ViThreeDimension/voron_trident_350/documentation_subpages/btt_octopus_pro_1.0_pins.png

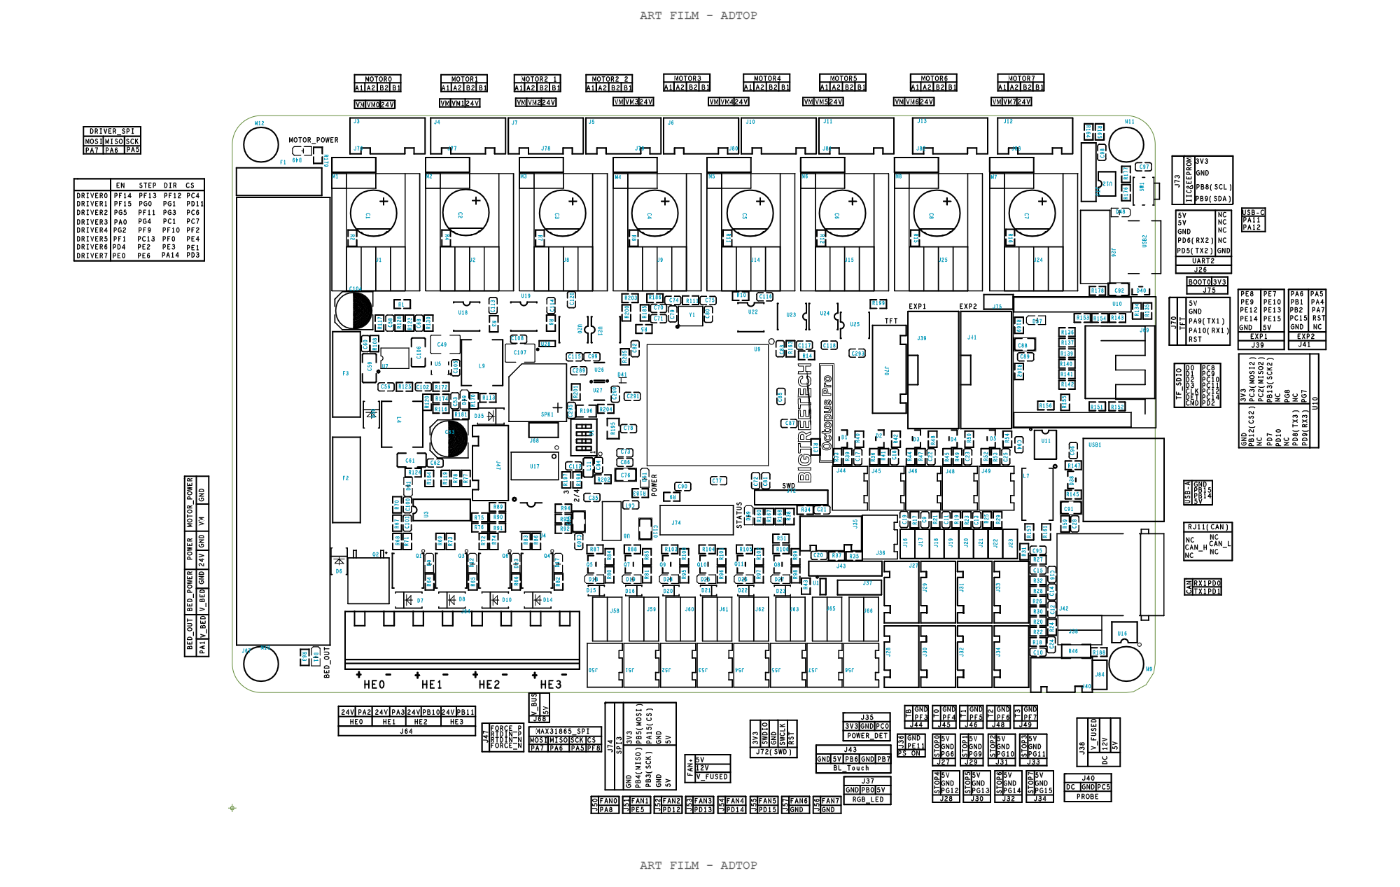
documentation_subpages/btt_octopus_pro_1.0_pins.png
