ViThreeDimension/voron_trident_350/mods/Sherpa_Mini-Extruder-master/Images/sherpa_mini_rc1.jpg

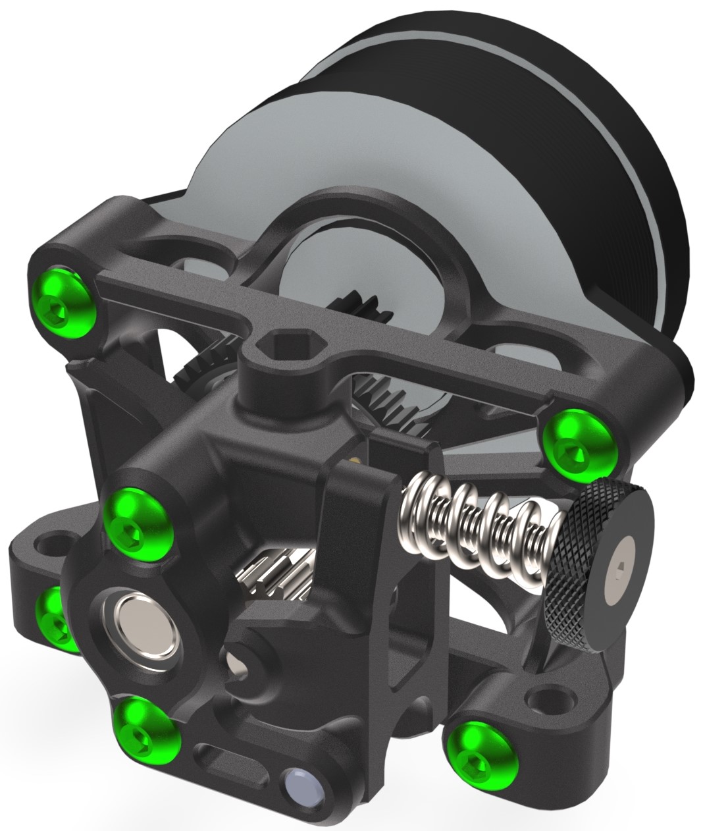
mods/Sherpa_Mini-Extruder-master/Images/sherpa_mini_rc1.jpg
