ViThreeDimension/voron_trident_350/mods/STH-36_sherpa_mini_mounting_plate_overmold_strain.stl

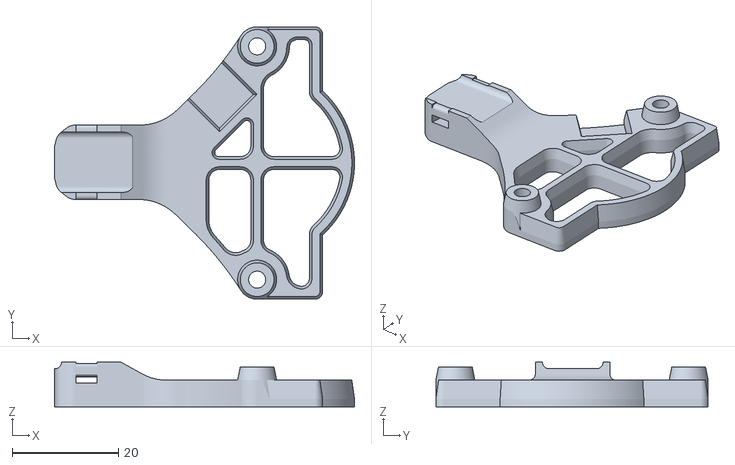
[picture p25: CAD file, 2022-10-18]
mods/STH-36_sherpa_mini_mounting_plate_overmold_strain.stl
56.4 x 51.2 x 8.36
