ViThreeDimension/voron_trident_350/mods/front panel handle/Front Panel - Handle Frame.3mf

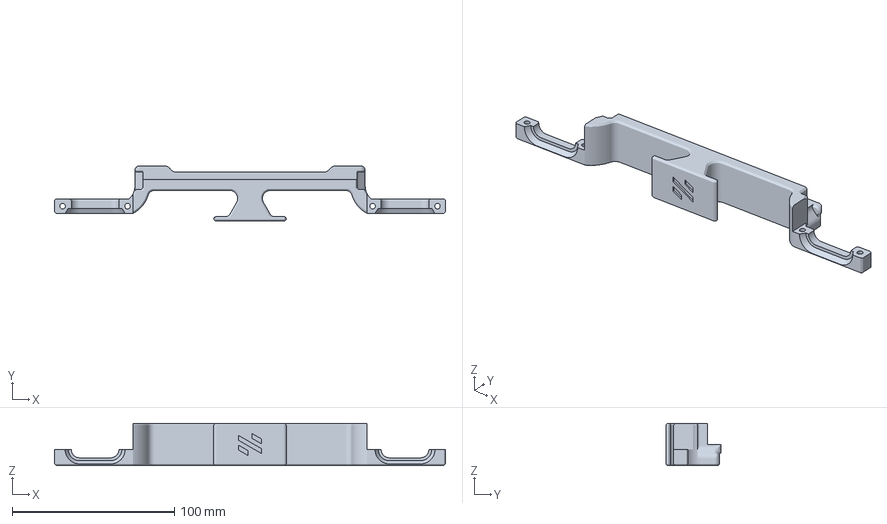
[picture p26: CAD file, 2022-12-22]
mods/front panel handle/Front Panel - Handle Frame.3mf
241.0 x 34.2 x 26.0 mm
