ViThreeDimension/voron_trident_350/mods/klickyNG/KlickyNG_Probe_Dock.stl

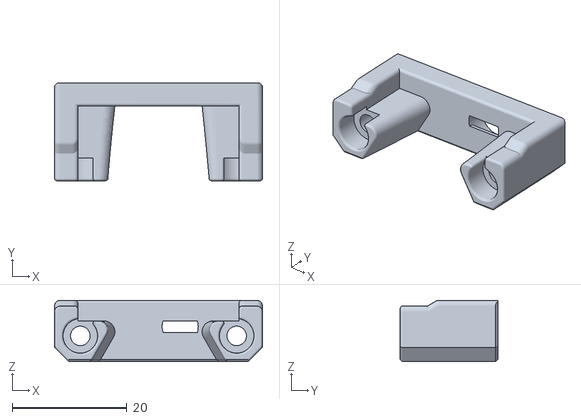
[picture p27: CAD file, 2022-10-18]
mods/klickyNG/KlickyNG_Probe_Dock.stl
36.3 x 17.0 x 10.7
