ViThreeDimension/voron_trident_350/mods/klickyNG/STL/2mm_extender.stl

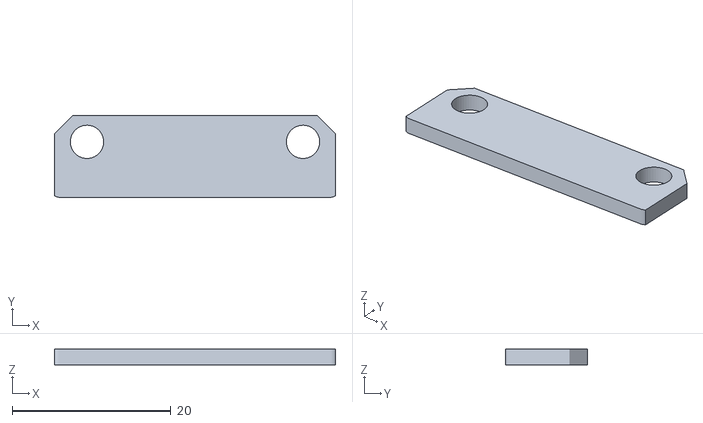
[picture p28: CAD file, 2022-10-18]
mods/klickyNG/STL/2mm_extender.stl
35.5 x 10.3 x 2.00
