ViThreeDimension/voron_trident_350/mods/own mods/Trident Carbon Pin Mod/a_drive_frame_upper_pinned.3mf

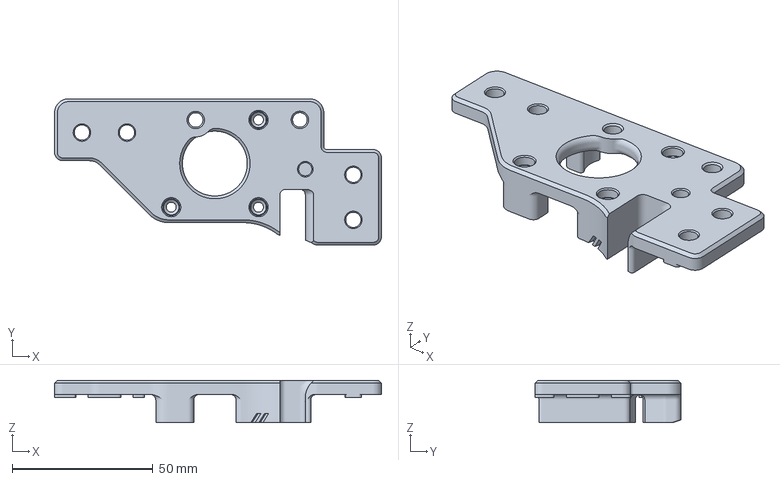
[picture p29: CAD file, 2022-10-18]
mods/own mods/Trident Carbon Pin Mod/a_drive_frame_upper_pinned.3mf
116.2 x 52.0 x 15.0 mm
