ViThreeDimension/voron_trident_350/mods/Panel_Locker/Locker_6mm.stl

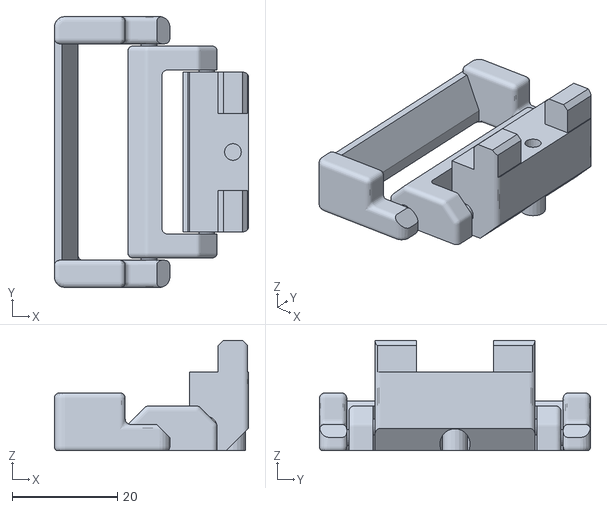
[picture p31: CAD file, 2022-10-18]
mods/Panel_Locker/Locker_6mm.stl
37.0 x 51.6 x 21.0
