ViThreeDimension/voron_trident_350/mods/Panel_Locker/step/Thin_PanelLocker.stp

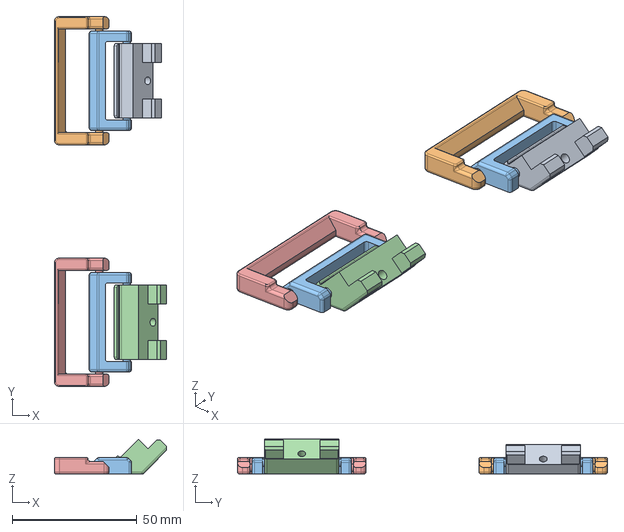
[picture p32: CAD file, 2022-10-18]
mods/Panel_Locker/step/Thin_PanelLocker.stp
45.1 x 148.6 x 13.9 mm
