ViThreeDimension/voron_trident_350/mods/Panel_Locker/Thin Locker/Thin_Locker_6.5mm.stl

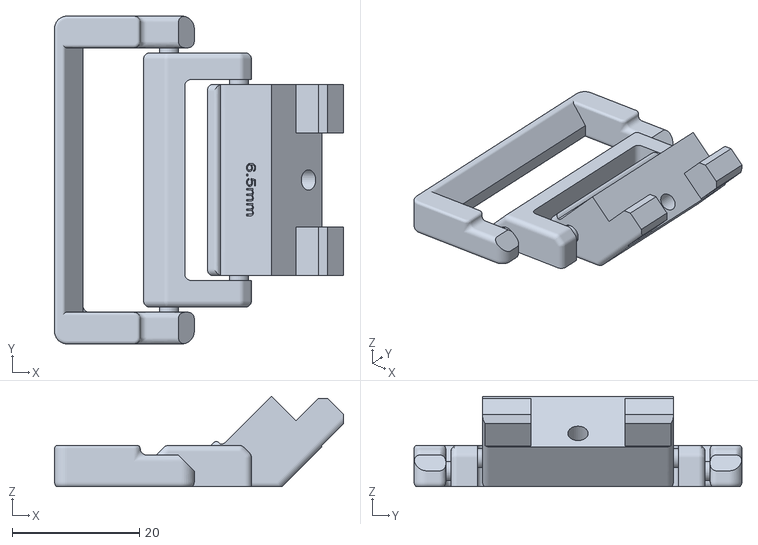
[picture p33: CAD file, 2022-10-18]
mods/Panel_Locker/Thin Locker/Thin_Locker_6.5mm.stl
45.5 x 51.6 x 14.2
