ViThreeDimension/voron_trident_350/mods/Sherpa_Mini-Extruder-master/Assembly_Tools/Shaft_Grinding_Tool/bottom.stl

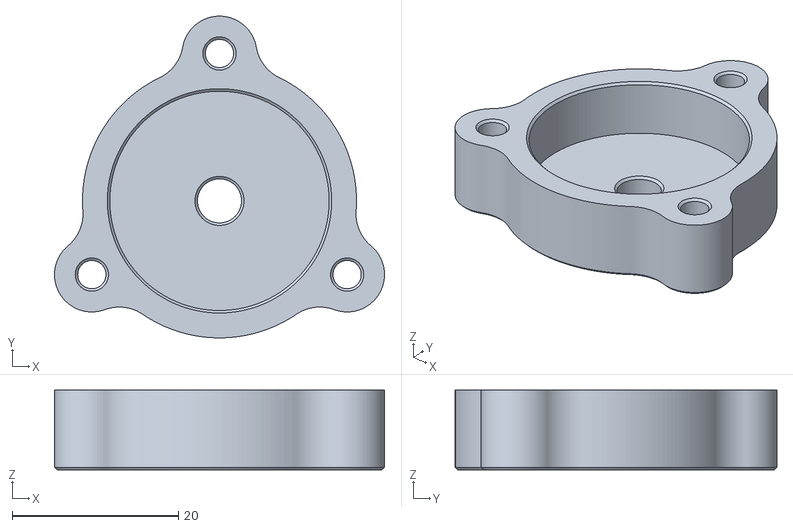
[picture p34: CAD file, 2022-10-18]
mods/Sherpa_Mini-Extruder-master/Assembly_Tools/Shaft_Grinding_Tool/bottom.stl
39.7 x 38.7 x 9.60
