ViThreeDimension/voron_trident_350/mods/Sherpa_Mini-Extruder-master/STLs/experimental_SLS+MJF_STLs/sls_[a]_idler_arm_long_x1_rev1.STL

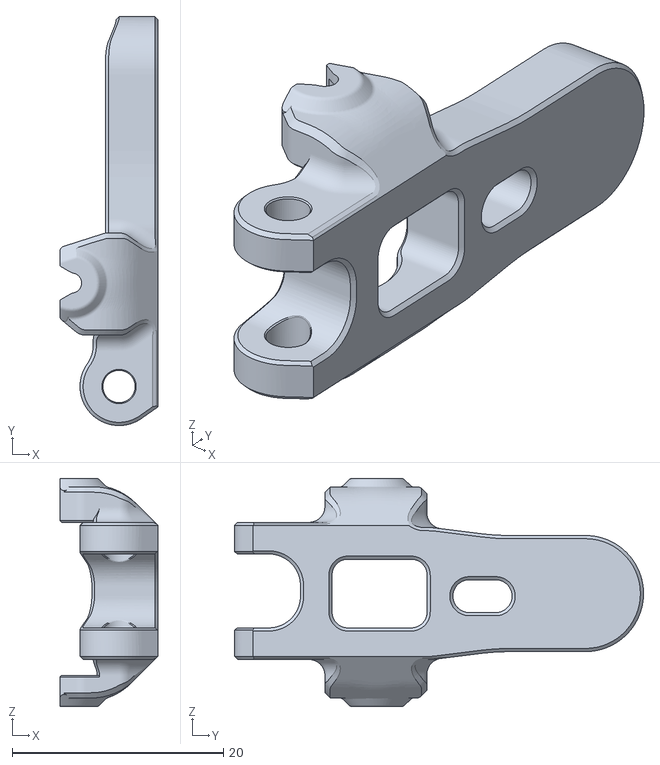
[picture p35: CAD file, 2022-10-18]
mods/Sherpa_Mini-Extruder-master/STLs/experimental_SLS+MJF_STLs/sls_[a]_idler_arm_long_x1_rev1.STL
9.30 x 38.8 x 21.6
