ViThreeDimension/voron_trident_350/mods/Sherpa_Mini-Extruder-master/STLs/FDM_STLs/optional_parts/rappel_adapter_x1_rev1.stl

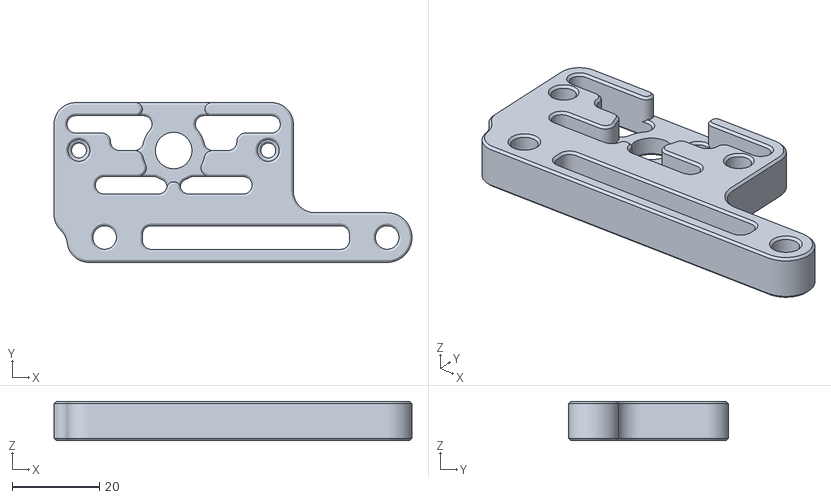
[picture p36: CAD file, 2022-10-18]
mods/Sherpa_Mini-Extruder-master/STLs/FDM_STLs/optional_parts/rappel_adapter_x1_rev1.stl
82.3 x 36.7 x 9.00
