ViThreeDimension/voron_trident_350/mods/front panel handle/panel vhb bottom.3mf

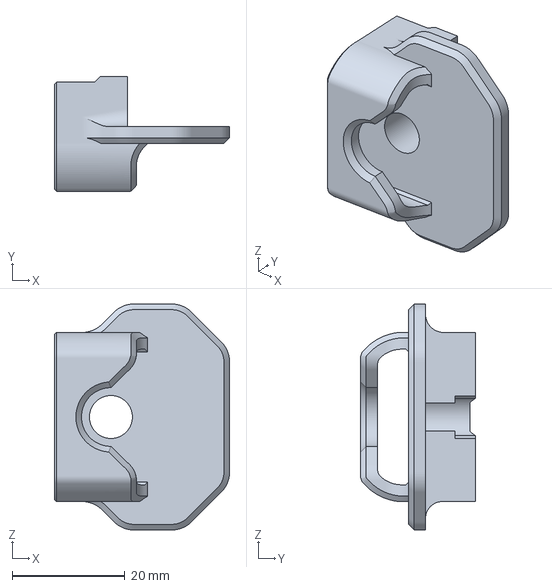
[picture p37: CAD file, 2022-12-22]
mods/front panel handle/panel vhb bottom.3mf
31.0 x 20.3 x 40.0 mm
