ViThreeDimension/voron_trident_350/mods/klickyNG/STL/KlickyNG_Tiny-M_mount_base.stl

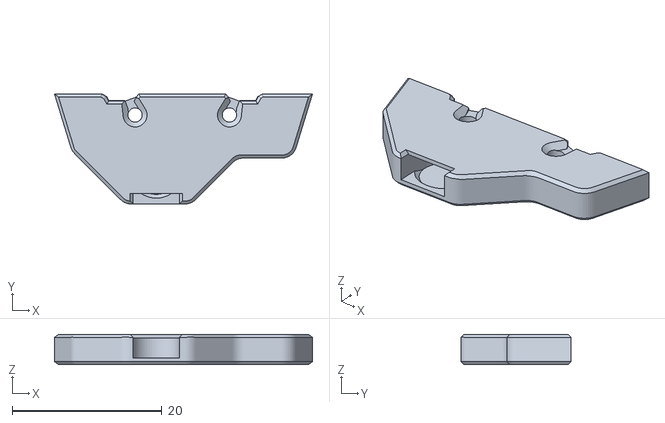
[picture p38: CAD file, 2022-10-18]
mods/klickyNG/STL/KlickyNG_Tiny-M_mount_base.stl
34.4 x 14.7 x 4.03
