ViThreeDimension/voron_trident_350/mods/own mods/RS25_psu_bracket_wide.step

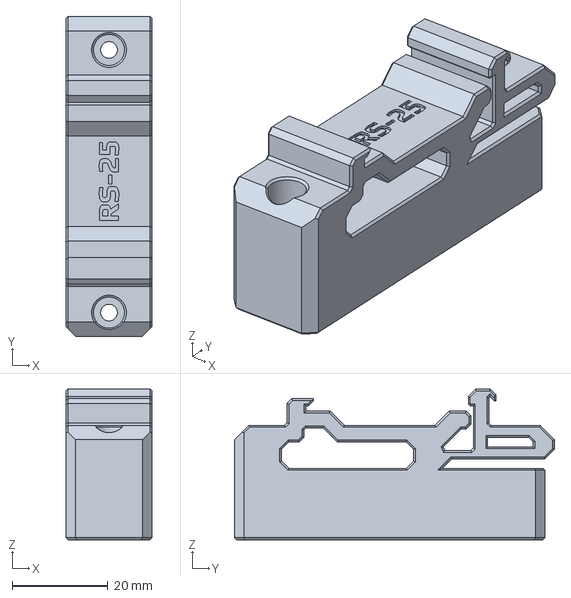
[picture p39: CAD file, 2022-12-22]
mods/own mods/RS25_psu_bracket_wide.step
18.0 x 67.0 x 31.6 mm
