ViThreeDimension/voron_trident_350/mods/own mods/Trident Pin Mod/STLs/b_drive_frame_lower_pinned.stl

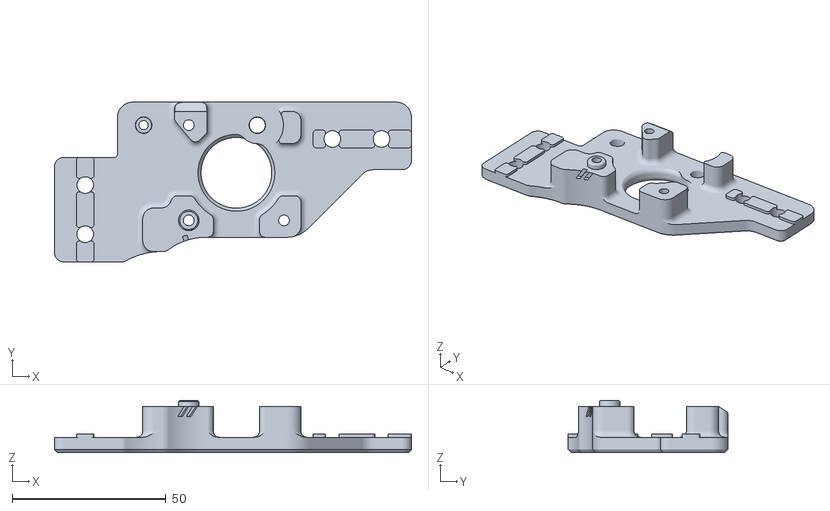
[picture p40: CAD file, 2022-10-18]
mods/own mods/Trident Pin Mod/STLs/b_drive_frame_lower_pinned.stl
116.2 x 52.0 x 17.0
