ViThreeDimension/voron_trident_350/mods/Panel_Locker/Thin Locker/Thin_Locker_5.5mm.stl

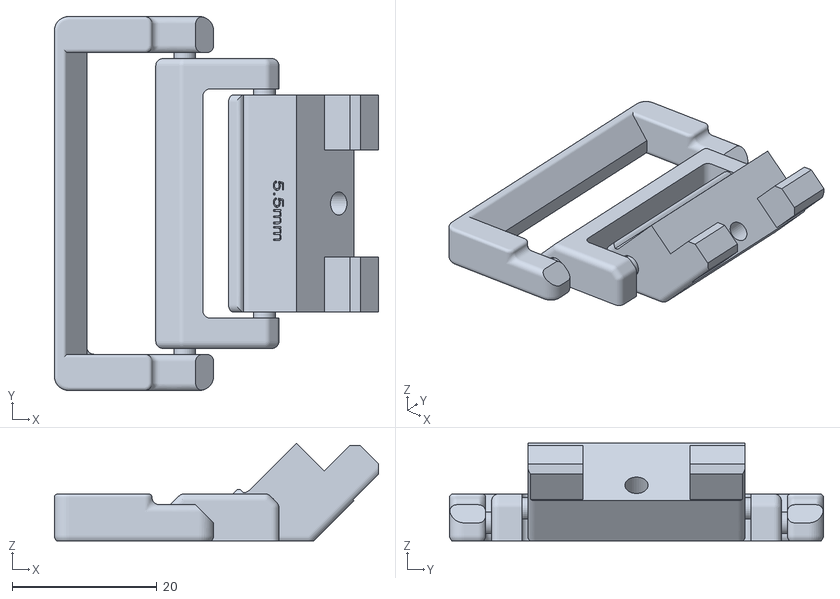
[picture p41: CAD file, 2022-10-18]
mods/Panel_Locker/Thin Locker/Thin_Locker_5.5mm.stl
44.8 x 51.6 x 13.5
