ViThreeDimension/voron_trident_350/mods/Sherpa_Mini-Extruder-master/Assembly_Tools/Shaft_Grinding_Tool/shaft_block v4.step

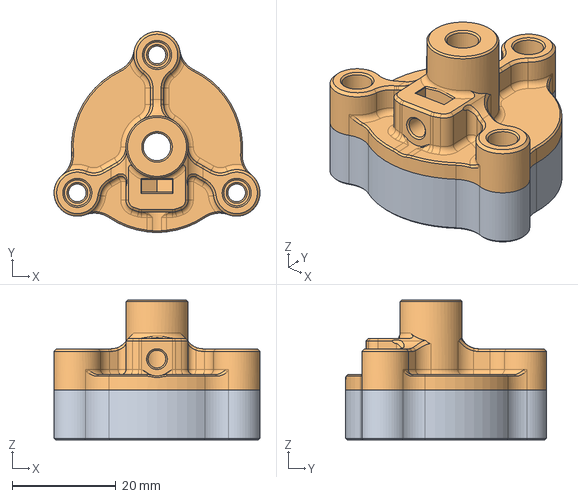
[picture p42: CAD file, 2022-10-18]
mods/Sherpa_Mini-Extruder-master/Assembly_Tools/Shaft_Grinding_Tool/shaft_block v4.step
39.8 x 38.8 x 27.0 mm
bottom
top
