ViThreeDimension/voron_trident_350/mods/Sherpa_Mini-Extruder-master/STLs/FDM_STLs/optional_parts/[a]_housing_front_k_x1_rev5.STL

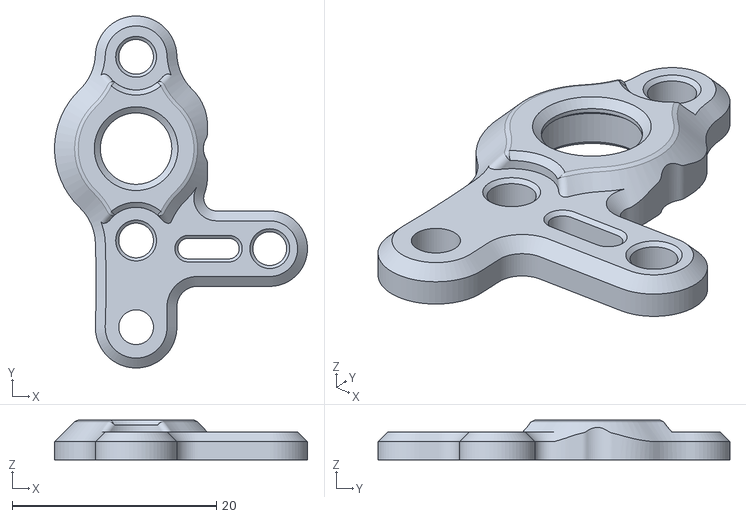
[picture p43: CAD file, 2022-10-18]
mods/Sherpa_Mini-Extruder-master/STLs/FDM_STLs/optional_parts/[a]_housing_front_k_x1_rev5.STL
24.8 x 34.5 x 3.90
