ViThreeDimension/voron_trident_350/mods/front panel handle/BottomFrontPanel_extraSized.3mf

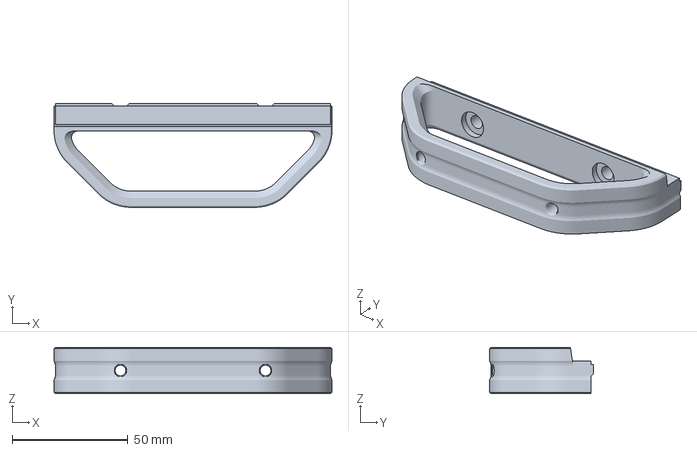
[picture p44: CAD file, 2022-12-22]
mods/front panel handle/BottomFrontPanel_extraSized.3mf
120.0 x 44.8 x 20.0 mm
