ViThreeDimension/voron_trident_350/mods/klickyNG/STL/KlickyNG_Probe_insert.stl

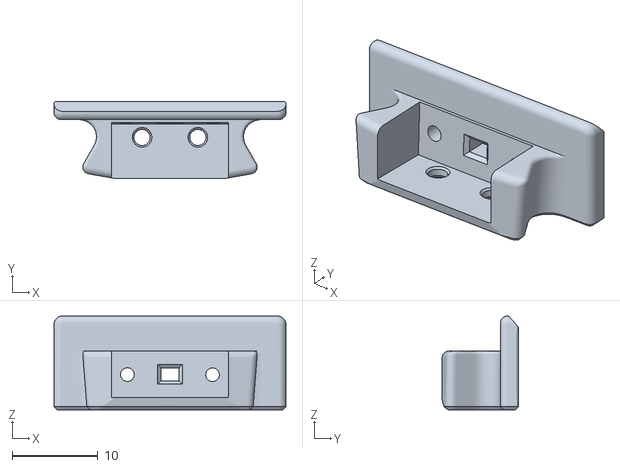
[picture p45: CAD file, 2022-10-18]
mods/klickyNG/STL/KlickyNG_Probe_insert.stl
27.0 x 8.97 x 11.0
