ViThreeDimension/voron_trident_350/mods/own mods/Trident Pin Mod/STLs/[a]_tensioner_left_pinned.stl

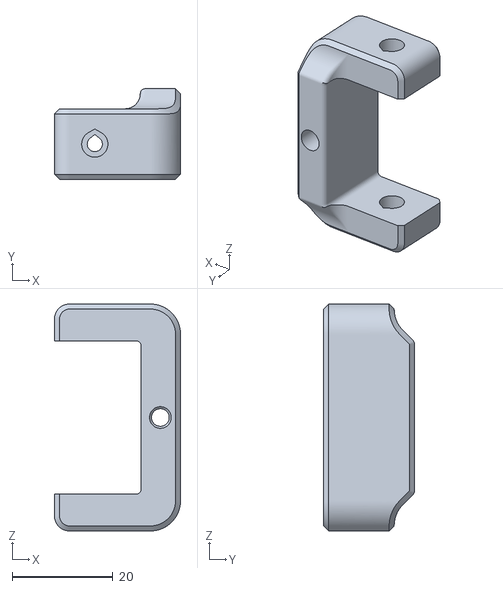
[picture p47: CAD file, 2022-10-18]
mods/own mods/Trident Pin Mod/STLs/[a]_tensioner_left_pinned.stl
25.0 x 18.0 x 45.0
