ViThreeDimension/voron_trident_350/mods/Panel_Locker/Thin Locker/Thin_Locker_3mm.stl

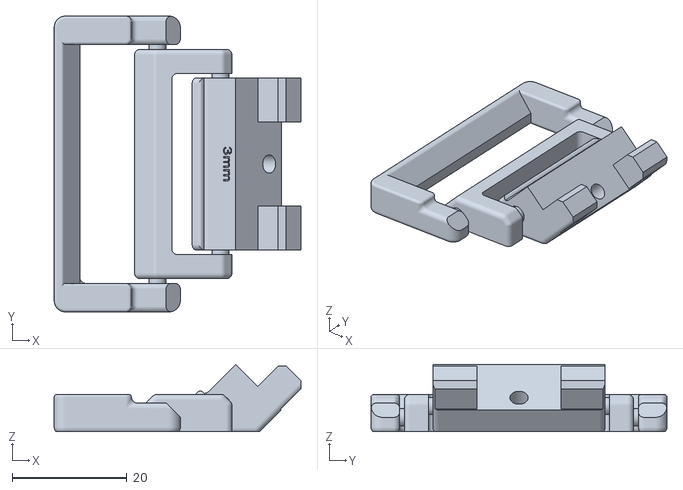
[picture p48: CAD file, 2022-10-18]
mods/Panel_Locker/Thin Locker/Thin_Locker_3mm.stl
43.0 x 51.6 x 11.7
