ViThreeDimension/voron_trident_350/mods/Sherpa_Mini-Extruder-master/STLs/FDM_STLs/housing_front_angled_front_brace.stl

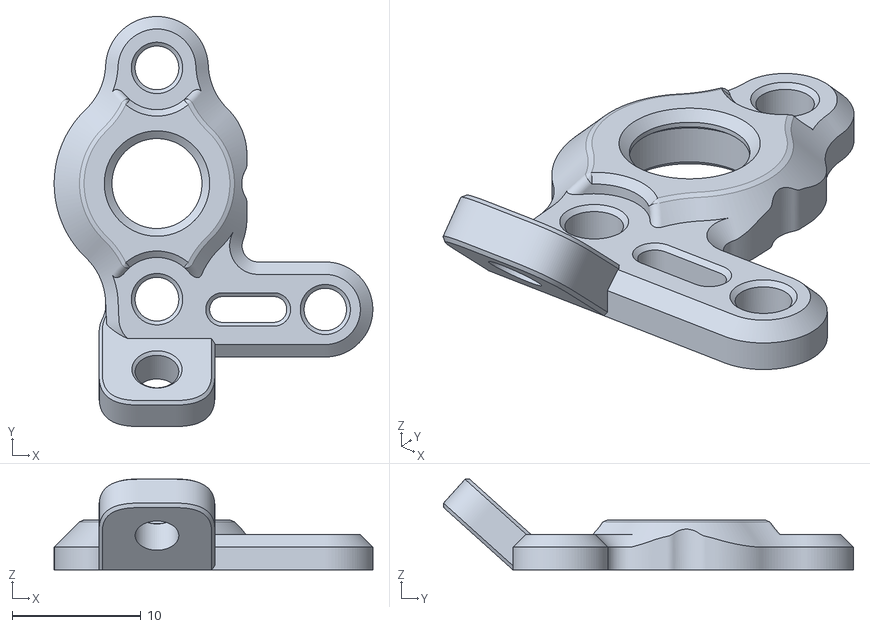
[picture p49: CAD file, 2022-10-18]
mods/Sherpa_Mini-Extruder-master/STLs/FDM_STLs/housing_front_angled_front_brace.stl
24.8 x 31.9 x 7.08
