ViThreeDimension/voron_trident_350/mods/Sherpa_Mini-Extruder-master/STLs/FDM_STLs/optional_parts/printable_sherpa_mini_gear_50t_sl_x1_rev1.stl

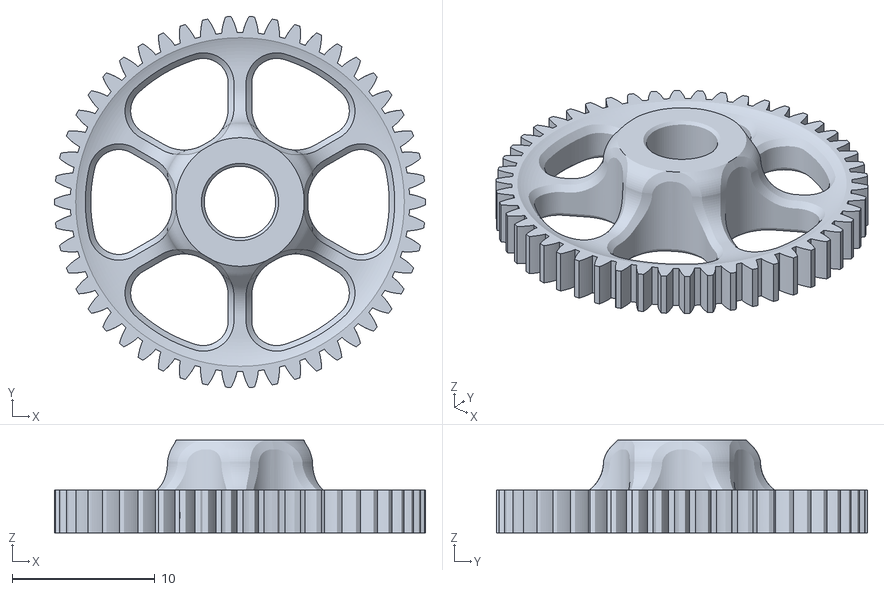
[picture p50: CAD file, 2022-10-18]
mods/Sherpa_Mini-Extruder-master/STLs/FDM_STLs/optional_parts/printable_sherpa_mini_gear_50t_sl_x1_rev1.stl
26.0 x 26.0 x 6.50
