ViThreeDimension/voron_trident_350/mods/front panel handle/Front Panel - RHS Latch.3mf

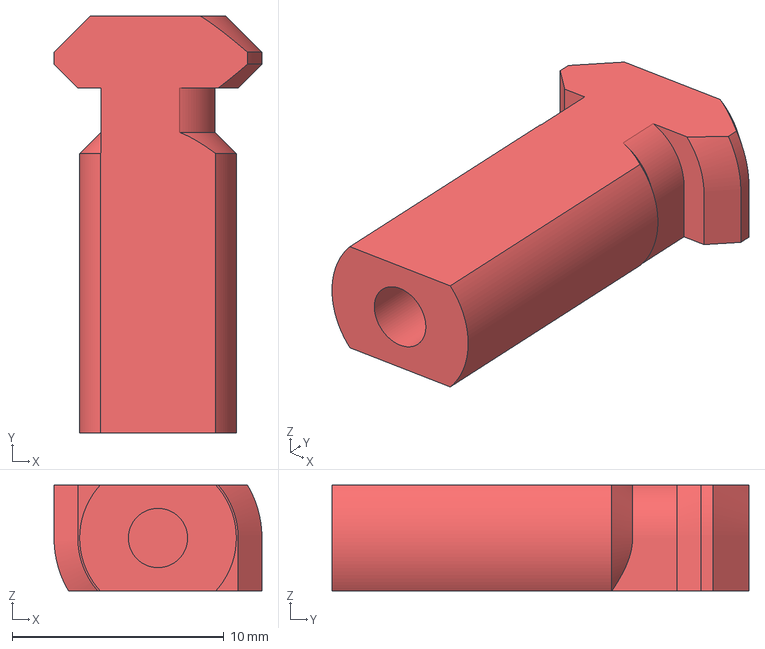
[picture p51: CAD file, 2022-12-22]
mods/front panel handle/Front Panel - RHS Latch.3mf
9.82 x 19.7 x 5.00 mm
