ViThreeDimension/voron_trident_350/mods/klickyNG/STL/KlickyNG_ABSB_mount_front.stl

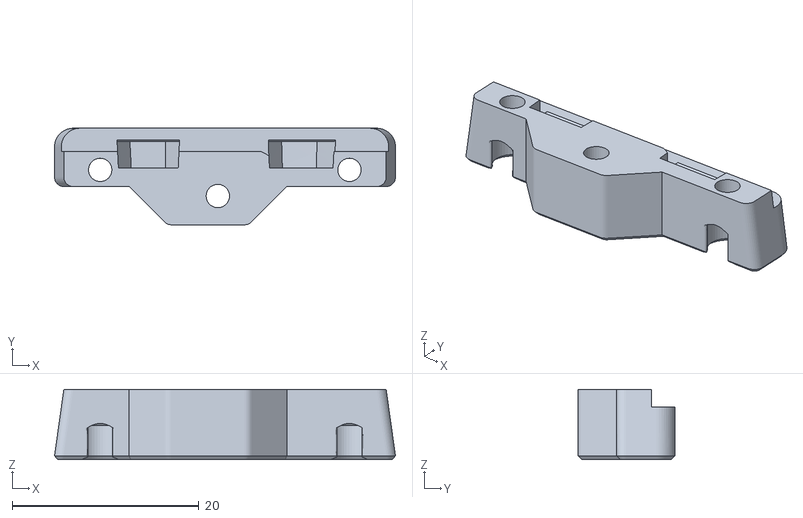
[picture p52: CAD file, 2022-10-18]
mods/klickyNG/STL/KlickyNG_ABSB_mount_front.stl
36.5 x 10.4 x 7.50
