ViThreeDimension/voron_trident_350/mods/Panel_Locker/Locker_3mm.stl

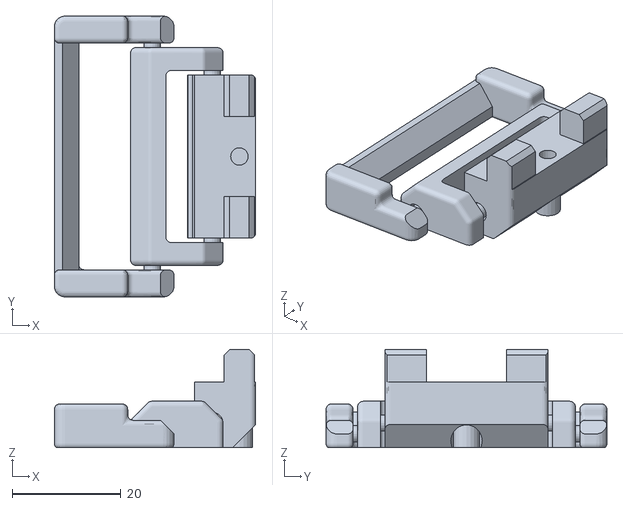
[picture p53: CAD file, 2022-10-18]
mods/Panel_Locker/Locker_3mm.stl
37.0 x 51.6 x 18.0
