ViThreeDimension/voron_trident_350/mods/Panel_Locker/Thin Locker/Thin_Locker_7.5mm.stl

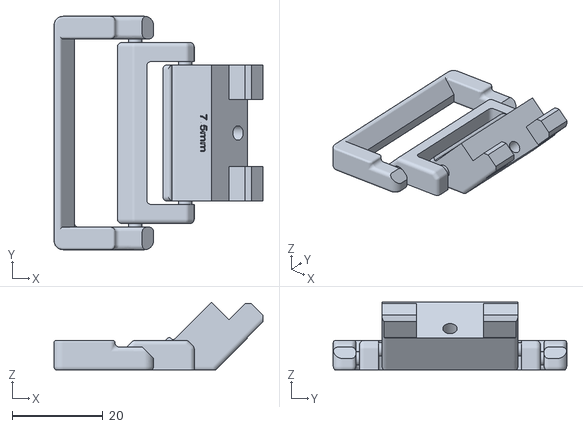
[picture p54: CAD file, 2022-10-18]
mods/Panel_Locker/Thin Locker/Thin_Locker_7.5mm.stl
46.2 x 51.6 x 14.9
