ViThreeDimension/voron_trident_350/mods/front panel handle/panel vhb.3mf

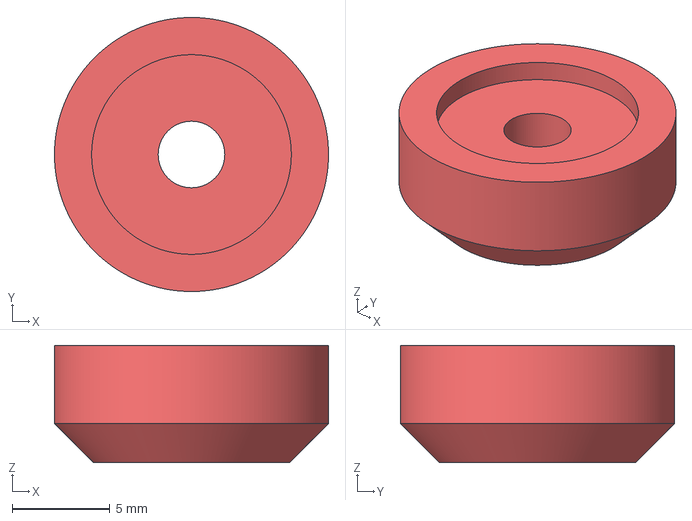
[picture p55: CAD file, 2022-12-22]
mods/front panel handle/panel vhb.3mf
14.0 x 14.0 x 6.00 mm
