ViThreeDimension/voron_trident_350/mods/own mods/Trident Pin Mod/STLs/xy_joint_left_upper_MGN12_pinned.stl

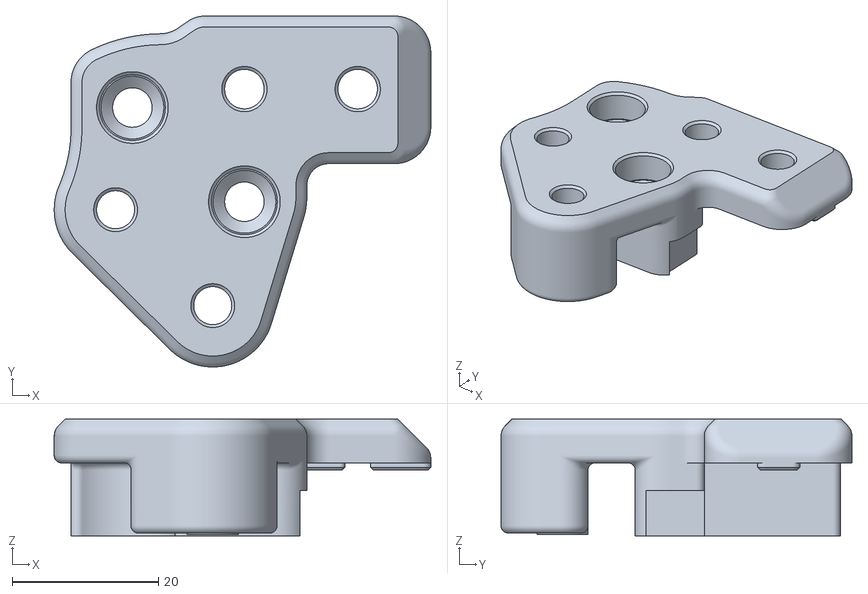
[picture p56: CAD file, 2022-10-18]
mods/own mods/Trident Pin Mod/STLs/xy_joint_left_upper_MGN12_pinned.stl
51.5 x 48.0 x 16.0
