ViThreeDimension/voron_trident_350/mods/Panel_Locker/Thin Locker/Thin_Locker_3.5mm.stl

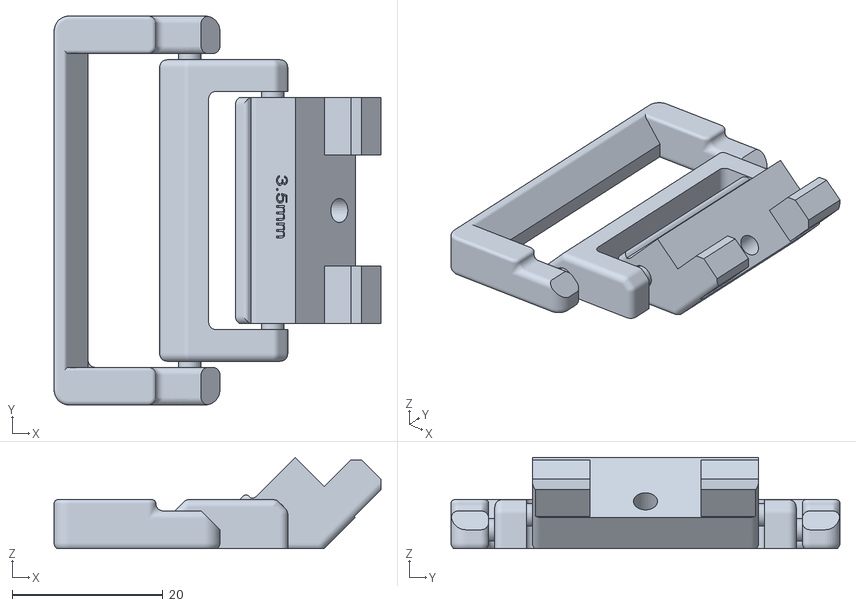
[picture p57: CAD file, 2022-10-18]
mods/Panel_Locker/Thin Locker/Thin_Locker_3.5mm.stl
43.4 x 51.6 x 12.1
