ViThreeDimension/voron_trident_350/mods/front panel handle/Front Panel - RHS Lever - with Pin.3mf

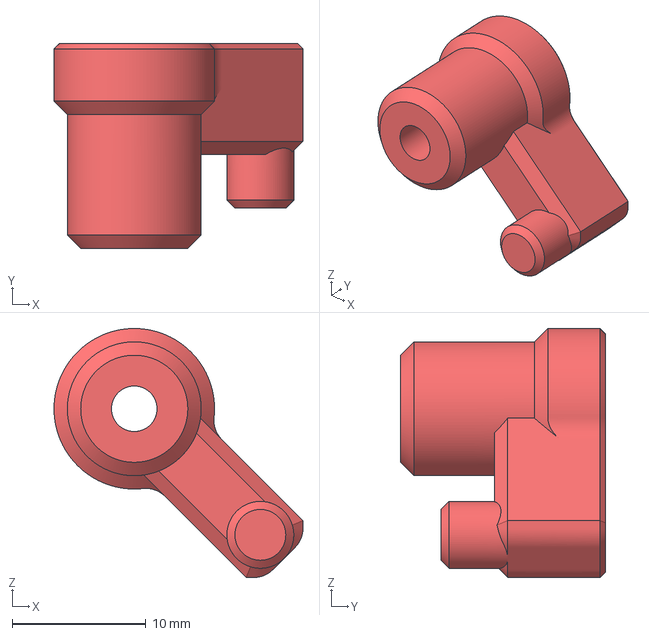
[picture p58: CAD file, 2022-12-22]
mods/front panel handle/Front Panel - RHS Lever - with Pin.3mf
18.6 x 15.3 x 18.6 mm
