ViThreeDimension/voron_trident_350/mods/Panel_Locker/Thin Locker/Thin_Locker_6mm.stl

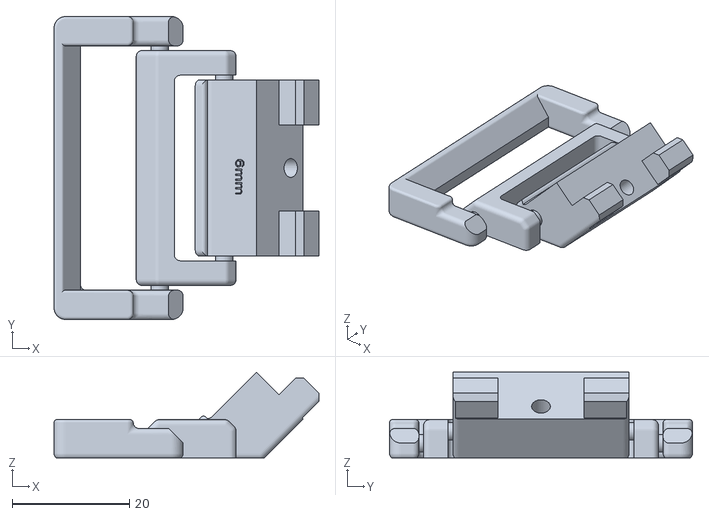
[picture p60: CAD file, 2022-10-18]
mods/Panel_Locker/Thin Locker/Thin_Locker_6mm.stl
45.1 x 51.6 x 14.6
