ViThreeDimension/voron_trident_350/mods/klickyNG/STL/KlickyNG_Tiny-M_mount_front.stl

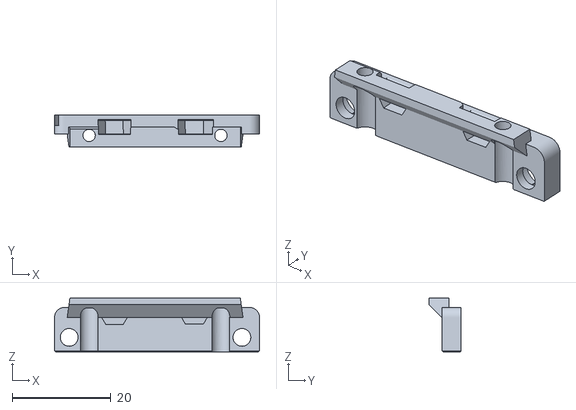
[picture p61: CAD file, 2022-10-18]
mods/klickyNG/STL/KlickyNG_Tiny-M_mount_front.stl
41.5 x 6.54 x 10.9
