ViThreeDimension/voron_trident_350/mods/Panel_Locker/Thin Locker/Thin_Locker_4.5mm.stl

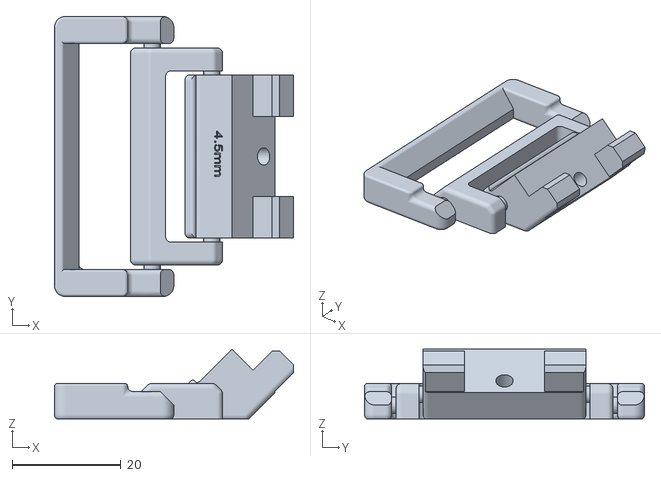
[picture p62: CAD file, 2022-10-18]
mods/Panel_Locker/Thin Locker/Thin_Locker_4.5mm.stl
44.1 x 51.6 x 12.8
