ViThreeDimension/voron_trident_350/mods/klickyNG/STL/KlickyNG_Probe_Helper_mount.stl

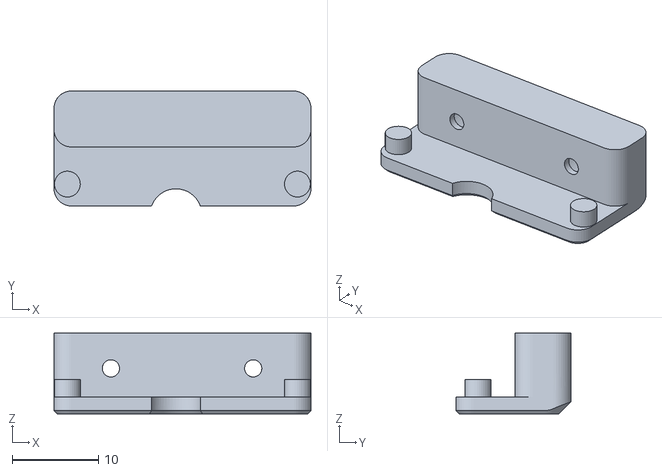
[picture p63: CAD file, 2022-10-18]
mods/klickyNG/STL/KlickyNG_Probe_Helper_mount.stl
29.8 x 13.3 x 9.40
