ViThreeDimension/voron_trident_350/mods/Panel_Locker/Thin Locker/Thin_Locker_4mm.stl

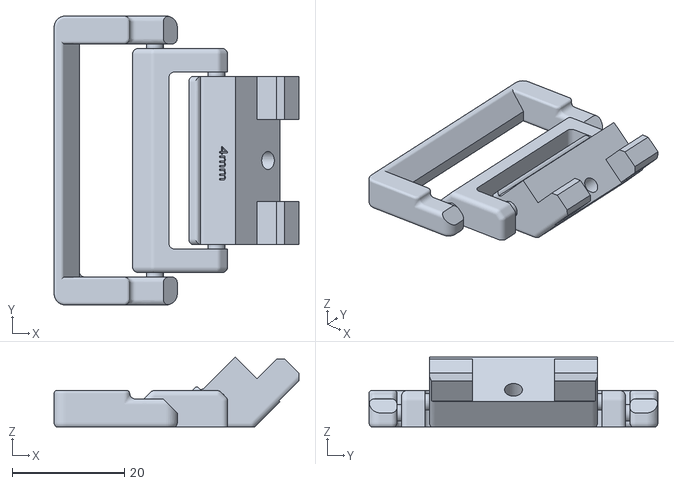
[picture p64: CAD file, 2022-10-18]
mods/Panel_Locker/Thin Locker/Thin_Locker_4mm.stl
43.7 x 51.6 x 12.5
