ViThreeDimension/voron_trident_350/mods/klickyNG/STL/KlickyNG_Probe_body.stl

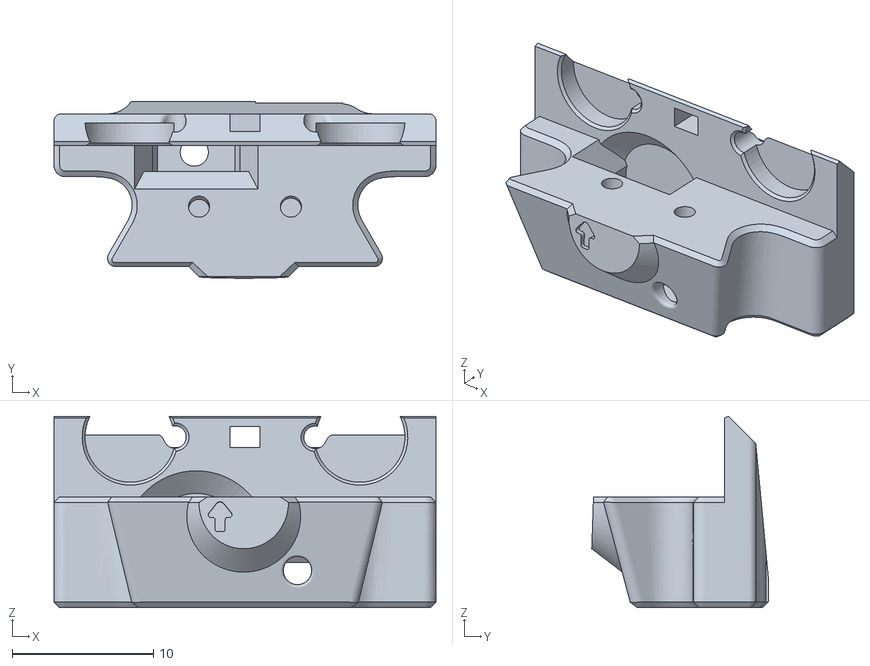
[picture p65: CAD file, 2022-10-18]
mods/klickyNG/STL/KlickyNG_Probe_body.stl
27.0 x 12.5 x 13.5
