ViThreeDimension/voron_trident_350/mods/Sherpa_Mini-Extruder-master/Assembly_Tools/Shaft_Grinding_Tool/tool_2.png

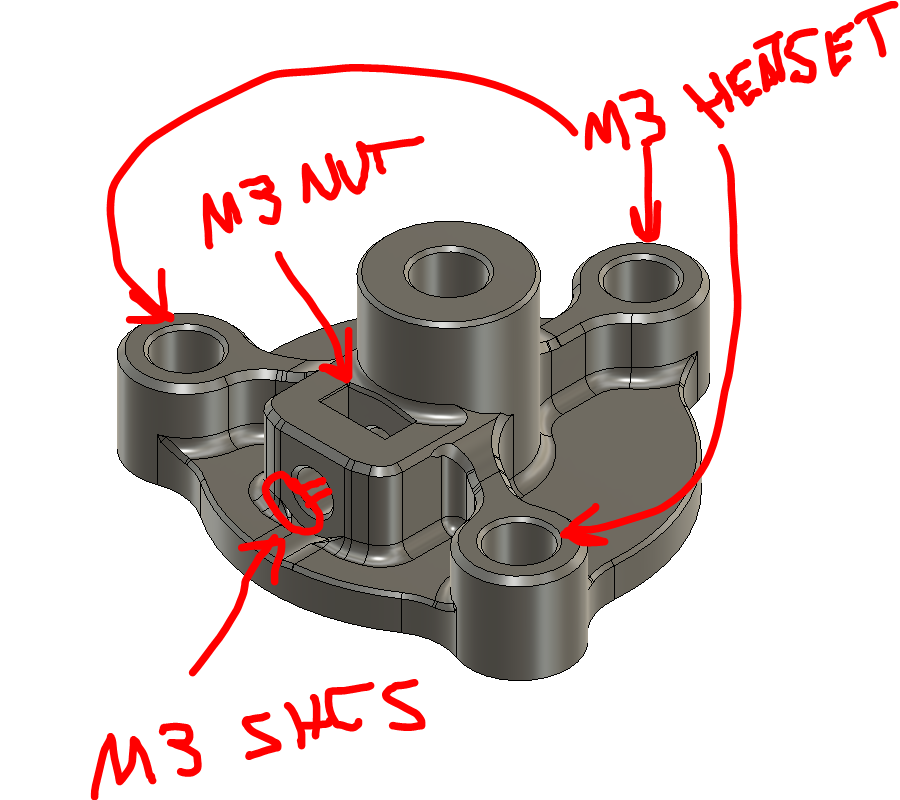
mods/Sherpa_Mini-Extruder-master/Assembly_Tools/Shaft_Grinding_Tool/tool_2.png
